tkqa1ex/SPRO-2/tests/dual_board_telemetry-load-1-test-3.csv.csv

Ctrl_Voltage_V | Ctrl_Current_mA | Ctrl_Temp_C | Gen_Voltage_V | Gen_Current_mA | Gen_Temp_C | RPM | I_mA_0 | T
2 | 233.2 | 28.84 | 0.02 | -0.03 | 24.61 | 4.166667 | 35.752167 | 1.325292 | 0
2 | 233.2 | 28.84 | 0.02 | -0.03 | 24.61 | 4.166667 | 35.752167 | 1.325292 | 0
2 | 232.8 | 28.84 | 0.02 | -0.02 | 24.61 | 4.166667 | 35.752167 | 1.325663 | 0
2.01 | 234 | 28.84 | 0.02 | -0.03 | 24.61 | 4.166667 | 35.752167 | 1.325292 | 0
7.27 | 465.6 | 28.84 | 6.53 | 14.99 | 24.61 | 1360.416667 | 41.177167 | 2.083802 | 0
7.69 | 333.2 | 28.84 | 9.74 | 43.39 | 24.61 | 2029.166667 | 43.852167 | 3.236684 | 0
11.44 | 493.2 | 28.84 | 14.8 | 59.22 | 24.61 | 3083.333333 | 48.068833 | 3.980416 | 0
11.95 | 448.8 | 28.84 | 15.72 | 71.55 | 24.61 | 3275 | 48.8355 | 4.466302 | 0
11.97 | 428.4 | 28.84 | 16.55 | 74.53 | 24.61 | 3447.916667 | 49.527167 | 4.602521 | 0
11.95 | 430.8 | 28.85 | 16.6 | 74.76 | 24.61 | 3458.333333 | 49.568833 | 4.6126 | 0
11.94 | 430.4 | 28.85 | 16.6 | 74.85 | 24.61 | 3458.333333 | 49.568833 | 4.615939 | 0
11.96 | 433.2 | 28.85 | 16.62 | 74.88 | 24.61 | 3462.5 | 49.5855 | 4.61767 | 0
11.96 | 430 | 28.85 | 16.66 | 75.01 | 24.61 | 3470.833333 | 49.618833 | 4.62373 | 0
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
