tkqa1ex/SPRO-2/tests/dual_board_telemetry-load-2&3-35degrees-1.csv

Ctrl_Voltage_V | Ctrl_Current_mA | Ctrl_Temp_C | Gen_Voltage_V | Gen_Current_mA | Gen_Temp_C | RPM | I_mA_0 | T
1.88 | 226.4 | 35.33 | 0.02 | -0.03 | 23.88 | 4.166667 | 35.752167 | 1.325292 | 0
1.88 | 226.4 | 35.33 | 0.02 | -0.03 | 23.88 | 4.166667 | 35.752167 | 1.325292 | 0
1.88 | 226.4 | 35.33 | 0.02 | -0.02 | 23.88 | 4.166667 | 35.752167 | 1.325663 | 0
1.88 | 226.4 | 35.33 | 0.02 | -0.03 | 23.88 | 4.166667 | 35.752167 | 1.325292 | 0
1.88 | 226.4 | 35.33 | 0.02 | -0.03 | 23.88 | 4.166667 | 35.752167 | 1.325292 | 0
1.88 | 226.4 | 35.32 | 0.02 | -0.03 | 23.88 | 4.166667 | 35.752167 | 1.325292 | 0
1.88 | 226.4 | 35.32 | 0.02 | -0.03 | 23.88 | 4.166667 | 35.752167 | 1.325292 | 0
1.88 | 226.4 | 35.32 | 0.02 | -0.03 | 23.88 | 4.166667 | 35.752167 | 1.325292 | 0
1.88 | 226.4 | 35.32 | 0.02 | -0.03 | 23.88 | 4.166667 | 35.752167 | 1.325292 | 0
1.88 | 226.4 | 35.31 | 0.02 | -0.03 | 23.88 | 4.166667 | 35.752167 | 1.325292 | 0
1.88 | 226.4 | 35.31 | 0.02 | -0.02 | 23.88 | 4.166667 | 35.752167 | 1.325663 | 0
1.88 | 226.4 | 35.31 | 0.02 | -0.02 | 23.88 | 4.166667 | 35.752167 | 1.325663 | 0
1.88 | 226.4 | 35.31 | 0.02 | -0.03 | 23.88 | 4.166667 | 35.752167 | 1.325292 | 0
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
