tkqa1ex/SPRO-2/tests/dual_board_telemetry-load-2&3-test-1.csv

Ctrl_Voltage_V | Ctrl_Current_mA | Ctrl_Temp_C | Gen_Voltage_V | Gen_Current_mA | Gen_Temp_C | RPM | I_mA_0 | T
4.98 | 439.2 | 28.66 | 2.97 | 0.07 | 24.76 | 618.75 | 38.2105 | 1.420207 | 0
7.36 | 327.2 | 28.66 | 9.31 | 10.68 | 24.76 | 1939.583333 | 43.493833 | 2.009849 | 0
9.68 | 383.2 | 28.66 | 11.94 | 13.87 | 24.76 | 2487.5 | 45.6855 | 2.209509 | 0
10.67 | 314.8 | 28.66 | 17.64 | 17.2 | 24.76 | 3675 | 50.4355 | 2.509277 | 0
11.96 | 352 | 28.66 | 19.4 | 18.44 | 24.77 | 4041.666667 | 51.902167 | 2.609694 | 0
11.94 | 324.8 | 28.67 | 20.42 | 20.57 | 24.77 | 4254.166667 | 52.752167 | 2.720252 | 0
11.95 | 324.8 | 28.67 | 20.44 | 20.65 | 24.77 | 4258.333333 | 52.768833 | 2.723839 | 0
11.96 | 326.8 | 28.67 | 20.44 | 20.65 | 24.77 | 4258.333333 | 52.768833 | 2.723839 | 0
11.95 | 326 | 28.67 | 20.4 | 20.62 | 24.77 | 4250 | 52.7355 | 2.721489 | 0
11.94 | 324.8 | 28.69 | 20.4 | 20.61 | 24.77 | 4250 | 52.7355 | 2.721118 | 0
11.95 | 324.8 | 28.69 | 20.39 | 20.6 | 24.77 | 4247.916667 | 52.727167 | 2.720438 | 0
11.97 | 326.4 | 28.69 | 20.41 | 20.62 | 24.77 | 4252.083333 | 52.743833 | 2.721798 | 0
11.96 | 326 | 28.69 | 20.39 | 20.61 | 24.77 | 4247.916667 | 52.727167 | 2.720809 | 0
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
