tkqa1ex/SPRO-2/tests/dual_board_telemetry-load-2&3-test-2.csv

Ctrl_Voltage_V | Ctrl_Current_mA | Ctrl_Temp_C | Gen_Voltage_V | Gen_Current_mA | Gen_Temp_C | RPM | I_mA_0 | T
1.89 | 247.2 | 23.48 | 0.02 | -0.03 | 23.38 | 4.166667 | 35.752167 | 1.325292 | 0
1.89 | 247.2 | 23.48 | 0.02 | -0.03 | 23.38 | 4.166667 | 35.752167 | 1.325292 | 0
1.89 | 247.2 | 23.48 | 0.02 | -0.03 | 23.38 | 4.166667 | 35.752167 | 1.325292 | 0
1.9 | 247.6 | 23.48 | 0.02 | -0.03 | 23.38 | 4.166667 | 35.752167 | 1.325292 | 0
6.86 | 378 | 23.48 | 8.06 | 5.01 | 23.38 | 1679.166667 | 42.452167 | 1.760846 | 0
9.95 | 352 | 23.49 | 15.01 | 13.78 | 23.38 | 3127.083333 | 48.243833 | 2.301084 | 0
11.51 | 335.2 | 23.49 | 17.82 | 19.09 | 23.38 | 3712.5 | 50.5855 | 2.584961 | 0
11.96 | 331.2 | 23.49 | 20.32 | 20.88 | 23.38 | 4233.333333 | 52.668833 | 2.728662 | 0
11.98 | 322.4 | 23.49 | 20.85 | 21.06 | 23.38 | 4343.75 | 53.1105 | 2.751726 | 0
11.99 | 322.4 | 23.49 | 20.85 | 21.04 | 23.38 | 4343.75 | 53.1105 | 2.750984 | 0
11.97 | 322.4 | 23.49 | 20.86 | 21.06 | 23.38 | 4345.833333 | 53.118833 | 2.752035 | 0
11.97 | 322 | 23.49 | 20.85 | 21.05 | 23.38 | 4343.75 | 53.1105 | 2.751355 | 0
11.96 | 322.8 | 23.49 | 20.79 | 21.02 | 23.38 | 4331.25 | 53.0605 | 2.748387 | 0
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
