tkqa1ex/SPRO-2/Heating and Cooling-code/include/usart.h

#ifndef USART_H_INCLUDED
#define USART_H_INCLUDED

int uart_putchar(char c, FILE *stream);
int uart_getchar(FILE *stream);

void uart_init(void);
void io_redirect(void);
int uart_getchar_nonblocking(char *c);
void uart_putchar2(char c);

#endif
